deckar01/3x3x3-cube-puzzle/settings/production.scad

piece_gap = .05;
resolution = 32;
