deckar01/3x3x3-cube-puzzle/settings/screw.scad

// #6-32 x 3/4-in Flat-Head
screw_head_thickness = 2.5;
screw_head_diameter = 6.5;
screw_diameter = 3.4;
